Akhipranav25/3rd_year_project/Lift_platform_1_bottom_slider.step

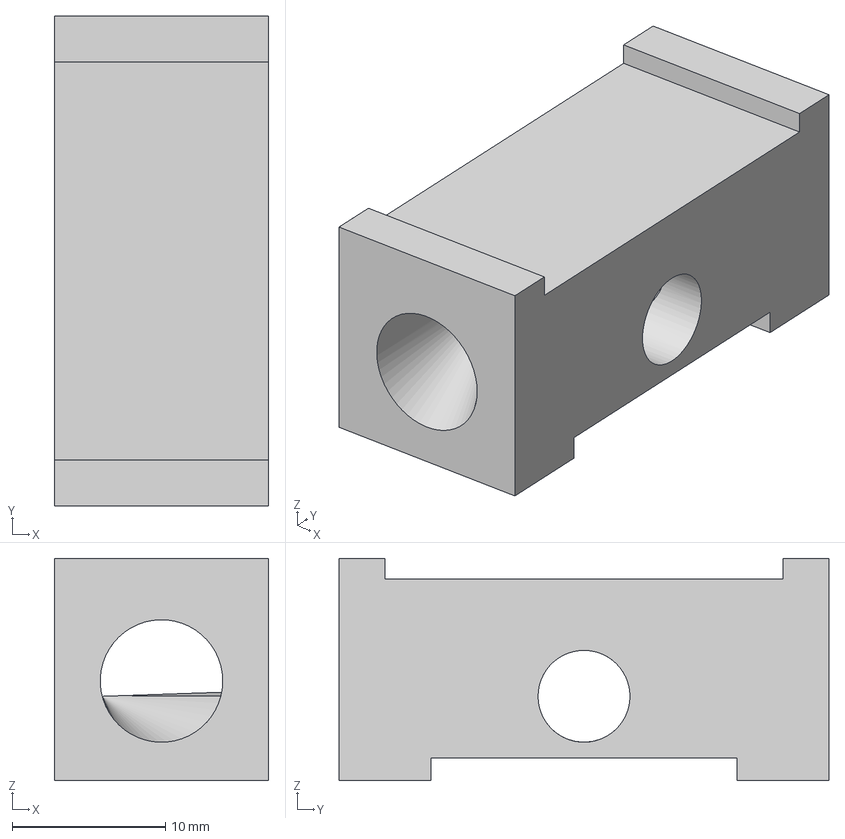
[picture p15: CAD file, 2026-04-20]
Lift_platform_1_bottom_slider.step
14.0 x 32.0 x 14.5 mm
