Akhipranav25/3rd_year_project/Lift_platform_1_arm_1.step

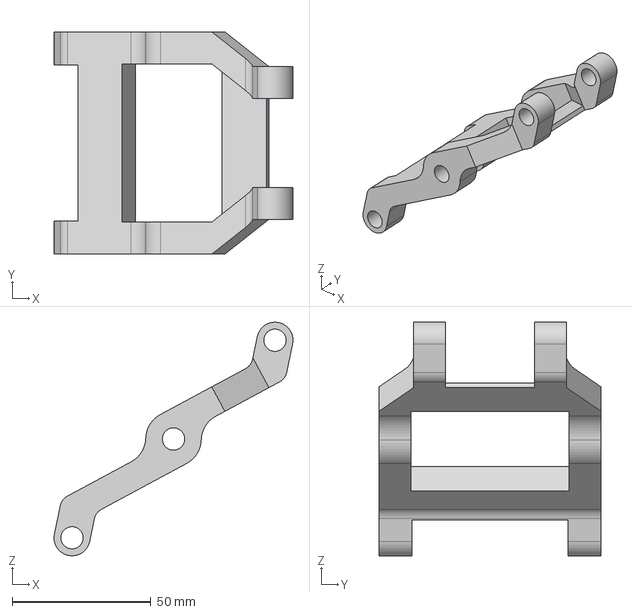
[picture p16: CAD file, 2026-04-20]
Lift_platform_1_arm_1.step
86.0 x 80.0 x 84.1 mm
