Akhipranav25/3rd_year_project/Lift_platform_1_bottom_housing.stl

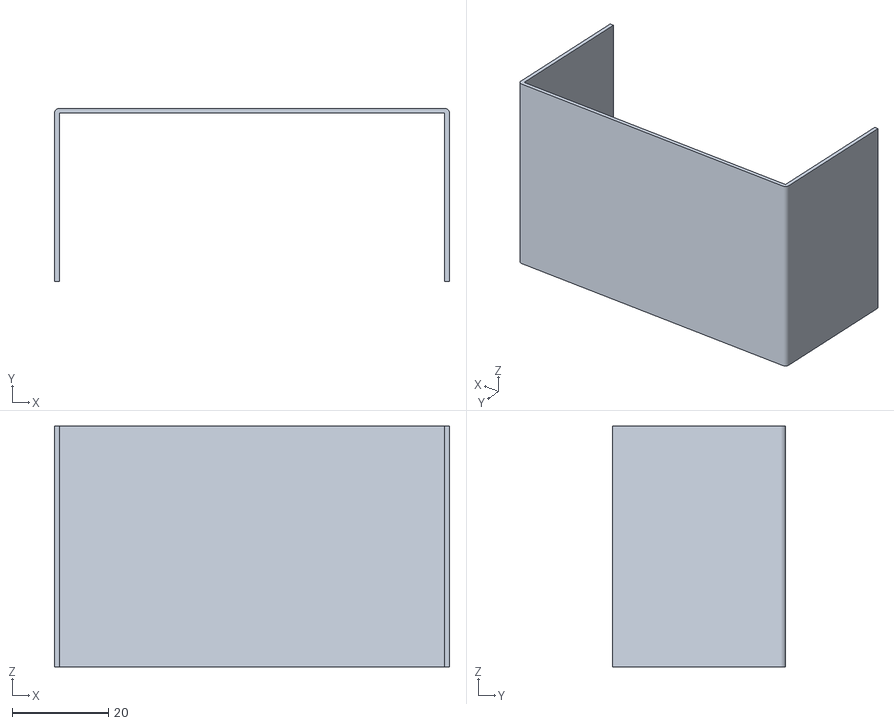
[picture p17: CAD file, 2026-04-20]
Lift_platform_1_bottom_housing.stl
82.0 x 36.0 x 50.0
