Akhipranav25/3rd_year_project/Lift_platform_1_top.stl

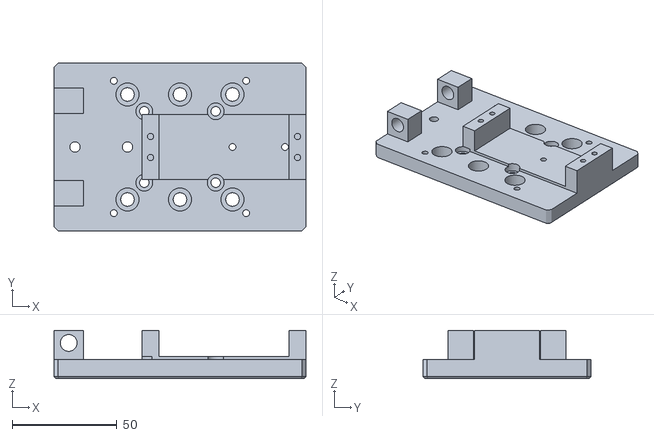
[picture p18: CAD file, 2026-04-20]
Lift_platform_1_top.stl
120.0 x 80.0 x 23.0
