Akhipranav25/3rd_year_project/Lift_platform_1_base.stl

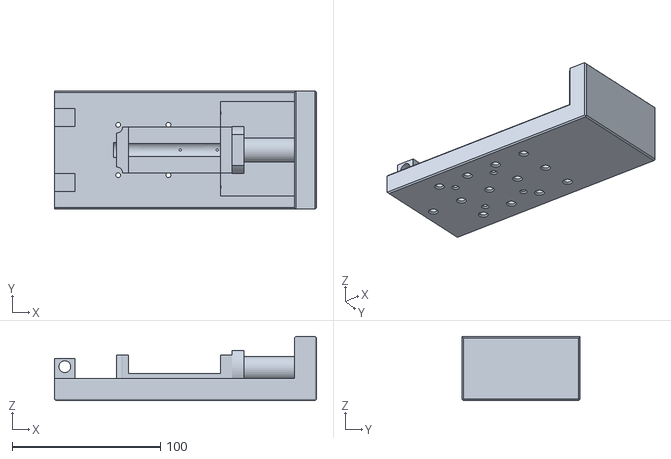
[picture p19: CAD file, 2026-04-20]
Lift_platform_1_base.stl
177.0 x 80.0 x 43.5
